asithniwantha/SmartCellAnalyzer/hardware/schematics/ChrgerDischarger.kicad_sch

## KiCad design hardware/schematics/ChrgerDischarger.kicad_sch (2025-10-13)

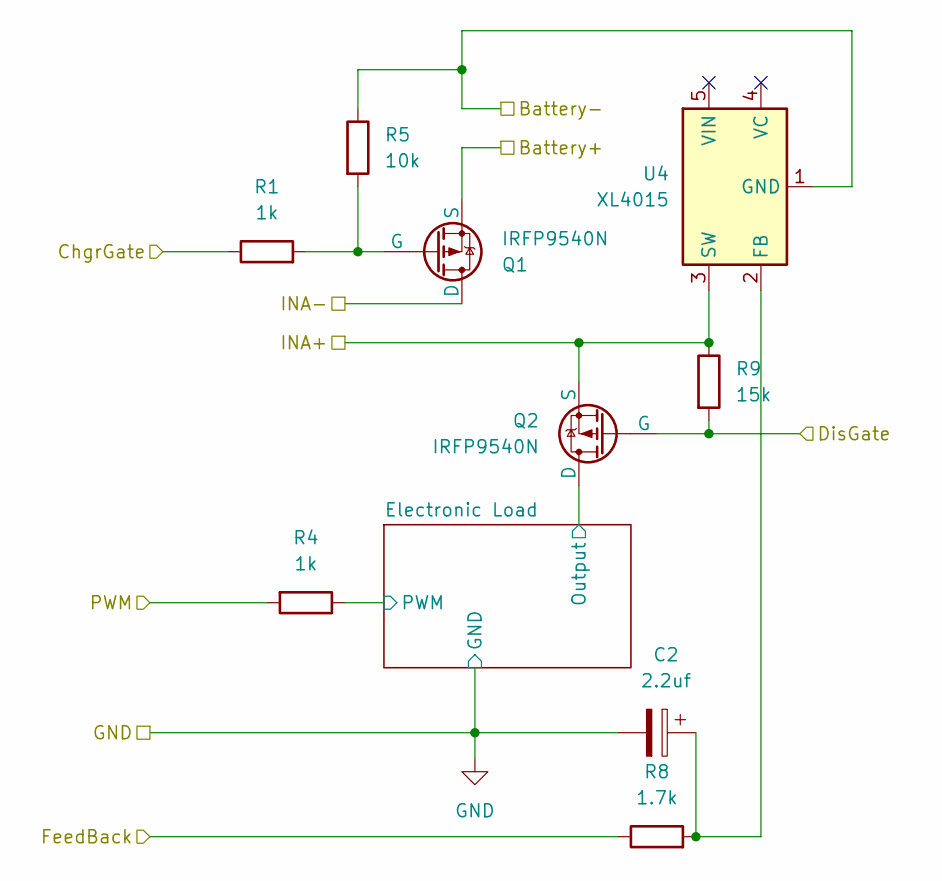
[picture p13: schematic ChrgerDischarger.kicad_sch]

Parts:
C2: 2.2uf
Q1, Q2: IRFP9540N
R1, R4: 1k
R5: 10k
R8: 1.7k
R9: 15k
U4: XL4015; TO-263-5_TabPin3

Connections:
Battery+: Q1.3 (S)
Battery-: R5.1, U4.1 (GND)
ChgrGate: R1.1
DisGate: Q2.2 (G), R9.2
FeedBack: R8.1
GND: C2.2
INA+: Q2.3 (S), R9.1, U4.3 (SW)
INA-: Q1.1 (D)
unnamed: C2.1, R8.2, U4.2 (FB)
unnamed: Q1.2 (G), R1.2, R5.2
Output: Q2.1 (D)
PWM: R4.1, R4.2
