asithniwantha/SmartCellAnalyzer/hardware/schematics/SmartCellAnalyzer.kicad_sch

## KiCad design hardware/schematics/SmartCellAnalyzer.kicad_sch (2025-10-13, an earlier design)

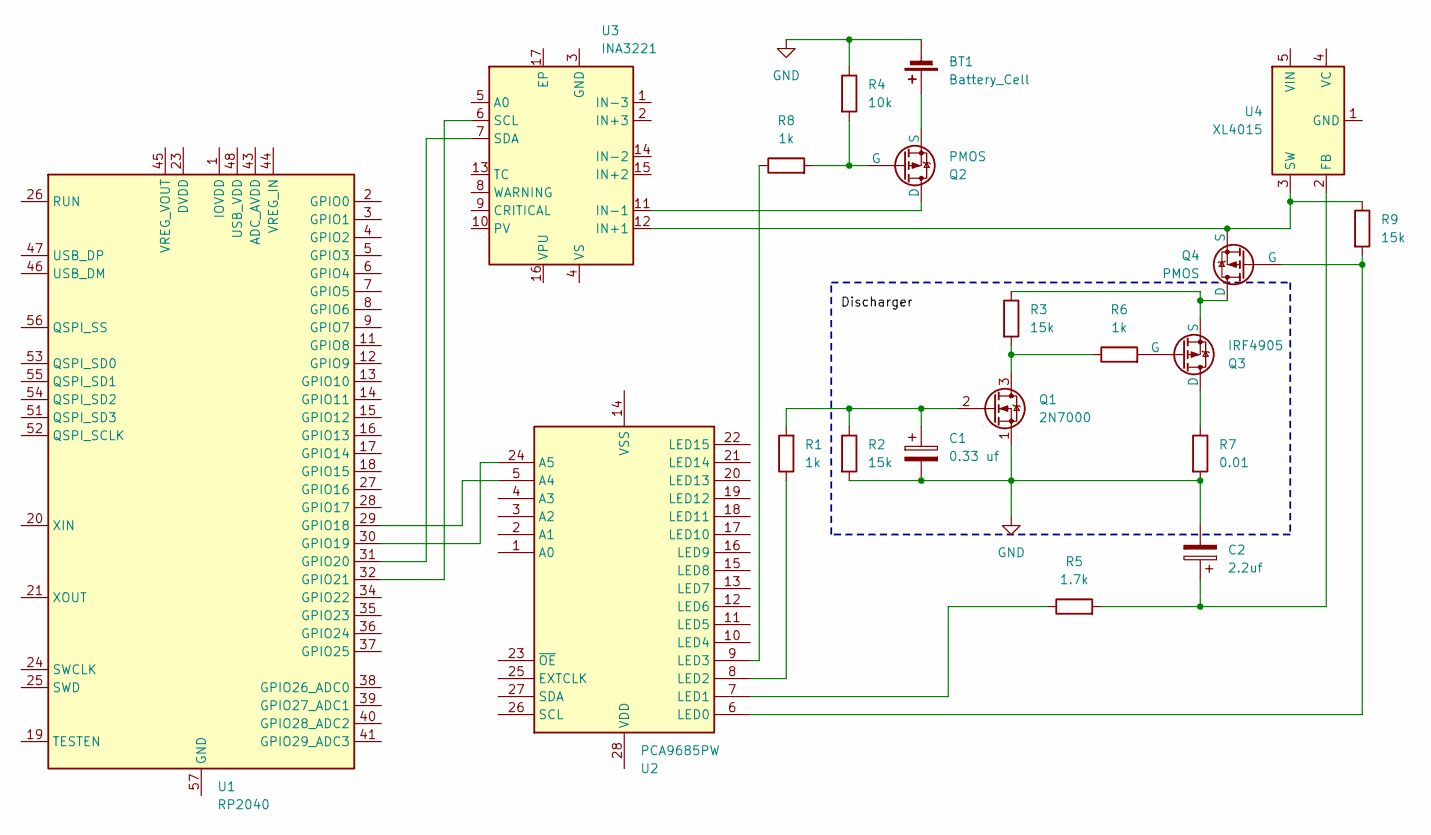
[picture p14: schematic SmartCellAnalyzer.kicad_sch]

Parts:
BT1: Battery_Cell
C1: 0.33 uf
C2: 2.2uf
Q1: 2N7000; TO-92_Inline
Q2, Q4: PMOS
Q3: IRF4905
R1, R6, R8: 1k
R2, R3, R9: 15k
R4: 10k
R5: 1.7k
R7: 0.01
U1: RP2040; QFN-56-1EP_7x7mm_P0.4mm_EP3.2x3.2mm
U2: PCA9685PW; TSSOP-28_4.4x9.7mm_P0.65mm
U3: INA3221; Texas_RGV0016A_VQFN-16-1EP_4x4mm_P0.65mm_EP2.1x2.1mm
U4: XL4015; TO-263-5_TabPin3

Connections:
GND: BT1.2 (-), C1.2, C2.2, Q1.1 (S), R2.2, R4.1, R7.2
unnamed: BT1.1 (+), Q2.3 (S)
unnamed: C1.1, Q1.2 (G), R1.2, R2.1
unnamed: C2.1, R5.2, U4.2 (FB)
unnamed: Q1.3 (D), R3.2, R6.1
unnamed: Q2.1 (D), U3.11 (IN-1)
unnamed: Q2.2 (G), R4.2, R8.2
unnamed: Q3.1 (D), R7.1
unnamed: Q3.2 (G), R6.2
unnamed: Q3.3 (S), Q4.1 (D), R3.1
unnamed: Q4.2 (G), R9.2, U2.6 (LED0)
unnamed: Q4.3 (S), R9.1, U3.12 (IN+1), U4.3 (SW)
unnamed: R1.1, U2.8 (LED2)
unnamed: R5.1, U2.7 (LED1)
unnamed: R8.1, U2.9 (LED3)
unnamed: U1.1 (IOVDD), U1.10 (IOVDD), U1.22 (IOVDD), U1.33 (IOVDD), U1.42 (IOVDD), U1.49 (IOVDD)
unnamed: U1.23 (DVDD), U1.50 (DVDD)
unnamed: U1.29 (GPIO18), U2.5 (A4)
unnamed: U1.30 (GPIO19), U2.24 (A5)
unnamed: U1.31 (GPIO20), U3.7 (SDA)
unnamed: U1.32 (GPIO21), U3.6 (SCL)
