asithniwantha/SmartCellAnalyzer/hardware/schematics/discharger.kicad_sch

## KiCad design hardware/schematics/discharger.kicad_sch (2025-10-13)

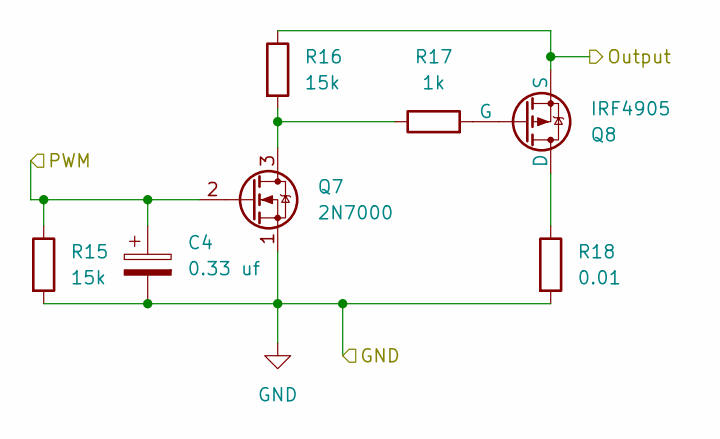
[picture p15: schematic discharger.kicad_sch]

Parts:
C4: 0.33 uf
Q7: 2N7000; TO-92_Inline
Q8: IRF4905
R15, R16: 15k
R17: 1k
R18: 0.01

Connections:
GND: C4.2, Q7.1 (S), R15.2, R18.2
unnamed: Q7.3 (D), R16.2, R17.1
unnamed: Q8.1 (D), R18.1
unnamed: Q8.2 (G), R17.2
Output: Q8.3 (S), R16.1
PWM: C4.1, Q7.2 (G), R15.1
